badges4dotcom/bsidesperth2025badge/PhysicalBadge/BSides/Game_Data.h

#include "Structures.h"

// Pins for the TFT screen.
#define TFT_CS     15
#define TFT_SCLK   14
#define TFT_DC     27     // Marked as A0 on TFT Display (Rev A: Pin 12, Rev B: 27)
#define TFT_MOSI   13
#define TFT_RST    4

// Pins for the SD Screen.
// Note: Confirmed working pins for RevB.
#define SD_CS   21
#define SD_SCLK 14
#define SD_MISO 12
#define SD_MOSI 13

// Pins for the button inputs.
#define UP_KEY_INPUT    25
#define DOWN_KEY_INPUT  26
#define A_KEY_INPUT     19
#define B_KEY_INPUT     18

// Bitwise registers for the button inputs.
#define UP_KEY_REGISTER   1
#define DOWN_KEY_REGISTER 2
#define A_KEY_REGISTER    4
#define B_KEY_REGISTER    8

// TFT Screen pixel width and height.
#define SCREEN_WIDTH  160
#define SCREEN_HEIGHT 128

// Constants for using a tilemap.
#define TILE_SIZE     				16			// Tile size (both width, and height)
#define TILEMAP_WIDTH 				208			// Width (px) for tilemap
#define TILEMAP_HEIGHT				144			// Height (px) for tilemap
#define TILE_FREEZONE_COLUMN	8				// Tiles in the "Free-zone" do not obstruct the character.
#define TILE_FREEZONE_ROW			4				// Any tile left of the 8th column tile, and above the 4th row, is in hte "free-zone".

#define MAP_SIZE_WIDTH	100						// Width of the map in tiles.
#define MAP_SIZE_HEIGHT	48						// Height of the map in tiles.

#define MAX_LINE_LENGTH   15					// Maximum length of line displayed on screen (used for text-wrapping).
#define MAX_MENUITEMS_ONSCREEN    4		// Maximum number of menu items to display on screen (main menu)
#define MAX_CHALLENGE_SEQUENCE	  60	// Maximum number of sequence items (for the offline challenge)
#define MAX_WIFI_NETWORKS         20	// Maximum number of WiFi networks to list.

#define ICON_SIZE								16		// Size of hte sequence item (offline challenge.)

#define BSIDES_BENNY_LOCATION_X			4		// Benny's character location (x, y) .
#define BSIDES_BENNY_LOCATION_Y			0
#define BSIDES_BENNY2_LOCATION_X		88	// Benny's character location for the petting zoo (x, y) .
#define BSIDES_BENNY2_LOCATION_Y		43

#define MAX_FIREWORKS     					5		// Max fireworks to display on the screen.
#define PARTICLE_LIFETIME 					30	// Firework particles lifetime.

// Game data for the animals in the game.
struct Animal animals[] = {
	{
		"Emu", "Emu", 32/16, 80/16, 1328 / 16, 272 / 16, 0, 0
	},
	{
		"Tasmanian Devil", "Devil", 312/16, 742/16, 1328 / 16, 336 / 16, 0, 0
	},
	{
		"Bob the Human", "Person7", 232/16, 422/16, 1328 / 16, 400 / 16, 0, 0
	},
	{
		"Kangaroo", "Kangaroo", 536/16, 202/16, 1328 / 16, 464 / 16, 0, 0
	},
	{
		"Parrot", "Parrot", 776/16, 678/16, 1328 / 16, 528 / 16, 0, 0
	},
	{
		"Blue Wren", "BlueWren", 596/16, 374/16, 1328 / 16, 592 / 16, 0, 0
	},
	{
		"Cockatoo", "Cockatoo", 1016/16, 54/16, 1328 / 16, 656 / 16, 0, 0
	},
	{
		"Koala", "Koala", 806 / 16, 40 / 16, 1536 / 16, 272 / 16, 0, 0
	},
	{
		"Snake", "Snake", -128 / 16, -128 / 16, 1536 / 16, 336 / 16, 0, 0
	},
	{
		"Spider", "Spider", -128 / 16, -128 / 16, 1536 / 16, 400 / 16, 0, 0
	},
	{
		"Dingo", "Dingo", -128 / 16, -128 / 16, 1536 / 16, 464 / 16, 0, 0
	},
	{
		"Wombat", "Wombat", -128 / 16, -128 / 16, 1536 / 16, 528 / 16, 0, 0
	},
	{
		"Kookaburra", "Kookaburra", -128 / 16, -128 / 16, 1536 / 16, 592 / 16, 0, 0
	},
	{
		"Echidna", "Echidna", -128 / 16, -128 / 16, 1536 / 16, 656 / 16, 0, 0
	}
};

// Game data for the challenges in the game.
const struct Challenge challenges[] = {
	{
		"Two-Timing Ted", "Person6", 56 / 16, 360 / 16, 16, 30, 8,
			{
				{"Person6", "Howdy partner. I'm Two-Timing Ted.",3},
				{"Null", "You be careful. A lot of animals around here have gone missing.",3},
				{"Null", "Anyway, challenge me if you dare!",3},
				{"Null", "",3}
			},
			{
				{"Person6", "Ah, you got me.",3},
				{"Null", "You've completed my challenge.",3},
				{"CyberEchidna", "Looks like your not the only two-timer on the block.",1},
				{"Person6", "I suppose not.",1}
			},
			{
				{"Person6", "Better luck next time.",3},
				{"Null", "",3},
				{"Null", "",3},
				{"Null", "",3}
			},
			{
				{100, "Sometimes if it doesn't work the first time..."},
				{80, "...You need to give it another go."},
				{60, "But timing is key."},
				{20, "You're not going to get the challenge if you stick around this long."}
			}
	},
	{
		"Guiding Gecko", "Person5", 920 / 16, 438 / 16, 20, 30, 9,
			{
				{"Person5", "Why hello there.",3},
				{"Null", "I'd like to GUIDE you through this challenge and this metaverse ..........",3},
				{"Null", "but I can't.",3},
				{"Null", "Good luck!",3}
			},
			{
				{"Person5", "Nice one! You have completed my challenge.",3},
				{"CyberEchidna", "Thanks. Now can you guide me to get the hell outta here??!!",3},
				{"Person5", "Mmmmm ... nah!",3},
				{"CyberEchidna", "Pfffftt!",3}
			},
			{
				{"Person5", "No luck this time.",3},
				{"Null", "Give it another try.",3},
				{"Null", "",3},
				{"Null", "",3}
			},
			{
				{100, "Something ain't right with this GUIDe."},
				{80, "He's a bit questionable."},
				{60, "You may need to find a Postman to fix it."},
				{40, "And post a correct GUIDe."}
			}
	},
	{
		"GP Gertrude", "Person3", 536 / 16, 740 / 16, 28, 30, 10,
			{
				{"Person3", "The doc is in.",3},
				{"Null", "I have the power to help you with this challenge.",3},
				{"Null", "It'd  be a real high for you to complete it.",1},
				{"Null", "",3}
			},
			{
				{"Person3", "You got it! Congratulations!",3},
				{"Null", "You haven't by any chance seen my husband Bob? He's been missing for a few days now.",3},
				{"CyberEchidna", "Ahhhhhh ..... no.",3},
				{"Person3", "Oh ok, I'm sure he'll turn up.",3}
			},
			{
				{"Person3", "No luck with the challenge this time.",3},
				{"Null", "I'm feeling pretty low.", 1},
				{"Null", "Nevermind though, it's like the 2nd time today.", 1},
				{"Null", "", 3}
			},
			{
				{100, "There are only four buttons in this game."},
				{80, "Yet five inputs have been enabled."},
				{60, "The code will give you the answer."},
				{20, "Look at the setup function in BSides.ono."}
			}
	},
	{
		"Sam D. Cornelius", "Person4", 170 / 16, 86 / 16, 42, 30, 11,
			{
				{"Person4", "Good day to you sir.",3},
				{"Null", "I am Sam D. Cornelius.",3},
				{"Null", "I seem to have lost my memories.",1},
				{"Null", "Can you help me find them?",1}
			},
			{
				{"Person4", "Oh, there they are. Thank you.",1},
				{"Person4", "You got the challenge.",3},
				{"Null", "Now on your way you.",3},
				{"CyberEchidna", "Farewell Sam D. Cornelius. I hope to always be in your memories.",1}
			},
			{
				{"Person4", "You didn't get the challenge this time.",3},
				{"Null", "Just like the animals around here, my memories seem to be non existant.",1},
				{"Null", "I'll be here all day.",1},
				{"Null", "",3}
			},
			{
				{100, "Sometimes this character goes by SD Cornelius"},
				{80, "You should check to see if he's given you a file"},
				{60, "And see if the file contents is correct"},
				{10, ""}
			}
	},
	{
		"Hidden Harriette", "Person2", 1096 / 16, 230 / 16, 50, 30, 12,
			{
				{"Person2", "How did you find me?",3},
				{"Null", "I thought I've been hiding better than all the animals around here.",3},
				{"Null", "My friend Bob was digging into where all the animals have gone, and now he's missing too.",3},
				{"Null", "Well, anyway, let's see if you can get my challenge.",3}
			},
			{
				{"Person2", "Gosh darn it.",3},
				{"Null", "Maybe I need to get better at hiding.",1},
				{"Null", "Well done on completing my challenge.",3},
				{"CyberEchidna", "Thanks. I was hide and seek champion three years running.",1}
			},
			{
				{"Person2", "No luck with the challenge this time.",3},
				{"Person2", "They don't call me Hidden Harriette for nothing.",1},
				{"Null", "",3},
				{"Null", "",3}
			},
			{
				{100,"This one is going to need a Postman"},
				{80,"Or a bug fix, recompile, and download."},
				{40,"In any case, it could get messy."},
				{10,""}
			}
	}
};

// The map for the game.
const int gameMap[MAP_SIZE_HEIGHT][MAP_SIZE_WIDTH] = {
{22,22,22,23,-1,78,80,13,14,15,16,17,-1,-1,-1,-1,-1,-1,-1,-1,44,45,46,-1,-1,-1,-1,-1,-1,-1,-1,-1,-1,-1,-1,-1,-1,-1,-1,-1,-1,-1,-1,-1,-1,78,80,-1,-1,-1,-1,-1,-1,-1,-1,-1,-1,-1,-1,-1,-1,91,79,79,79,79,79,79,79,79,79,79,79,79,79,79,79,79,79,93,78,80,-1,-1,-1,-1,-1,-1,-1,-1,-1,-1,-1,-1,-1,-1,-1,-1,-1,-1},
{35,35,35,36,-1,91,93,26,27,28,29,30,-1,-1,-1,-1,-1,-1,-1,-1,57,58,59,-1,-1,-1,-1,-1,-1,-1,-1,-1,-1,-1,-1,-1,-1,-1,-1,-1,-1,-1,-1,-1,-1,91,93,-1,-1,-1,-1,-1,-1,44,45,46,-1,-1,-1,-1,-1,91,92,105,105,105,105,105,105,105,105,105,105,105,105,105,105,105,92,93,91,93,-1,-1,-1,-1,-1,-1,-1,-1,-1,-1,-1,-1,-1,-1,-1,-1,-1,-1},
{-1,34,35,36,-1,91,93,39,40,41,42,43,-1,-1,-1,-1,-1,-1,-1,-1,70,71,72,-1,-1,-1,-1,-1,-1,-1,-1,-1,-1,-1,-1,-1,-1,-1,-1,-1,-1,-1,-1,-1,-1,91,93,-1,-1,-1,-1,-1,-1,57,58,59,-1,-1,-1,-1,-1,91,93,-1,-1,-1,-1,-1,-1,-1,-1,-1,-1,-1,-1,44,45,46,91,93,91,93,-1,-1,-1,-1,-1,-1,-1,-1,-1,-1,-1,-1,-1,-1,-1,-1,-1,-1},
{-1,34,35,36,-1,91,93,52,53,54,55,56,60,-1,-1,-1,-1,-1,-1,-1,-1,-1,-1,-1,-1,21,22,22,22,22,22,22,22,22,22,22,22,22,22,22,22,22,23,-1,-1,91,93,-1,-1,-1,-1,-1,-1,70,71,72,-1,-1,-1,-1,-1,91,93,-1,-1,-1,-1,-1,-1,-1,-1,-1,-1,-1,-1,57,58,59,91,93,91,93,-1,-1,-1,-1,-1,-1,-1,-1,-1,-1,-1,-1,-1,-1,-1,-1,-1,-1},
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
{-1,34,35,36,-1,-1,-1,-1,-1,-1,-1,-1,-1,-1,-1,-1,78,80,34,35,36,-1,70,71,72,-1,-1,-1,-1,-1,-1,-1,-1,-1,-1,-1,-1,-1,-1,-1,-1,-1,-1,91,93,-1,34,35,25,48,48,48,48,48,48,48,48,48,49,-1,-1,-1,91,93,-1,-1,91,93,-1,-1,-1,-1,57,58,59,91,93,34,35,36,91,92,105,105,105,105,92,93,-1,-1,-1,-1,91,92,105,105,105,105,92,93},
{-1,34,35,36,-1,-1,78,80,-1,-1,-1,-1,-1,-1,-1,-1,91,93,34,35,12,22,22,22,22,22,22,22,22,22,22,22,22,22,22,22,22,22,22,23,-1,-1,-1,91,93,-1,47,48,49,-1,-1,-1,-1,-1,-1,-1,-1,-1,-1,-1,-1,-1,91,92,79,79,92,93,-1,-1,-1,-1,70,71,72,91,93,34,35,36,91,93,-1,-1,-1,-1,91,93,-1,-1,-1,-1,91,93,-1,-1,-1,-1,91,93},
{-1,34,35,36,-1,-1,91,93,-1,-1,-1,-1,-1,-1,-1,-1,91,93,34,35,35,35,35,35,35,35,35,35,35,35,35,35,35,35,35,35,35,35,35,36,-1,-1,-1,91,93,-1,-1,-1,-1,-1,-1,-1,78,80,-1,-1,-1,-1,-1,-1,-1,-1,104,105,105,105,105,106,-1,-1,-1,-1,-1,-1,-1,91,93,34,35,36,91,93,-1,-1,-1,-1,91,93,-1,-1,-1,-1,91,93,-1,-1,-1,-1,91,93},
{-1,34,35,36,-1,-1,91,93,-1,-1,-1,-1,-1,-1,-1,-1,91,93,47,48,48,48,48,48,48,48,48,48,48,48,48,48,48,48,48,48,48,24,35,36,-1,-1,-1,91,93,-1,-1,-1,-1,-1,-1,-1,91,93,-1,-1,-1,-1,-1,-1,-1,-1,-1,-1,-1,-1,-1,-1,-1,-1,-1,-1,-1,-1,-1,91,93,34,35,36,91,92,79,79,79,79,92,93,-1,-1,-1,-1,91,92,79,79,79,79,92,93},
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
};

// Definitions required for Online Challenges.
char* GAME_WEB_URL = "badge.bsidesperth.com.au";
char* GAME_ROOT_CERTIFICATE = \
"-----BEGIN CERTIFICATE-----\n" \
"MIIEGzCCAwOgAwIBAgIULYVISFG3QsBjY+rdPtSzc/bA4hQwDQYJKoZIhvcNAQEL\n" \
"BQAwgZwxCzAJBgNVBAYTAkFVMRowGAYDVQQIDBFXZXN0ZXJuIEF1c3RyYWxpYTEO\n" \
"MAwGA1UEBwwFUGVydGgxFTATBgNVBAoMDEJTaWRlcyBQZXJ0aDEhMB8GA1UEAwwY\n" \
"YmFkZ2UuYnNpZGVzcGVydGguY29tLmF1MScwJQYJKoZIhvcNAQkBFhhhZG1pbkBi\n" \
"c2lkZXNwZXJ0aC5jb20uYXUwHhcNMjUxMDE3MDE1ODE3WhcNMjYxMDE3MDE1ODE3\n" \
"WjCBnDELMAkGA1UEBhMCQVUxGjAYBgNVBAgMEVdlc3Rlcm4gQXVzdHJhbGlhMQ4w\n" \
"DAYDVQQHDAVQZXJ0aDEVMBMGA1UECgwMQlNpZGVzIFBlcnRoMSEwHwYDVQQDDBhi\n" \
"YWRnZS5ic2lkZXNwZXJ0aC5jb20uYXUxJzAlBgkqhkiG9w0BCQEWGGFkbWluQGJz\n" \
"aWRlc3BlcnRoLmNvbS5hdTCCASIwDQYJKoZIhvcNAQEBBQADggEPADCCAQoCggEB\n" \
"AKhhTlis1jlzda90e7ueb6dc7XlPJJdcV3fNfwi2+jSr2BVRGpUgWcsspCC+cxSy\n" \
"d9wv0Lr60v+ccpxxLAPtAxR48KrmVZs4FraxJTnCfyebFnHT4p/vNmBaNvrnKZXQ\n" \
"aHe+EBjNE14J4OXet9EannqkWA0cuOIMqQiDGYAGwJFSP6bgIh6L1F0s+eXr8F2l\n" \
"1OomFlVebRJ0Iu89hi7E+KohI/cqvv8UgaqLgF9rTgyxmdlCf7U33GKIf7Cq0p24\n" \
"34KhDgse64Ge2AFpZv3kpGbAy8nSmLG37LdcSD9Df2L5ysOM5XJGxwYmwmgj7uhI\n" \
"oHVl72/a5a3N3i5fjx2Jr8kCAwEAAaNTMFEwHQYDVR0OBBYEFGDpsNiHHIQKmhDM\n" \
"rSFdu90t3cfrMB8GA1UdIwQYMBaAFGDpsNiHHIQKmhDMrSFdu90t3cfrMA8GA1Ud\n" \
"EwEB/wQFMAMBAf8wDQYJKoZIhvcNAQELBQADggEBAG52x7Ly3pixucy2iKD4GfUj\n" \
"E3uNZZVUNSY9omg1DKZt+BZXB9MVlwvJ+VYmdatSi+gBP2nz50ISpz4aFAHT3ex4\n" \
"35GU/YALRiUQhTQ+EmiNxQ2EjBQG7hgj/c6E89IHbDqQdDXe7zclo4SmYPuFo4uX\n" \
"LYn917K0cE391gtj1vxajw/HXRkyWZlv0WdffnCzFilfy006QLs9qEy8K8OY9rnk\n" \
"q+Eoritwj3cVzLdpvZpUnEZrOsMlEKrMP8DsWu/PaCw9nSybek5f2oA1topLOCTl\n" \
"iZ/kkfc6/mhgGSVODRJQaog8xuqh+6XDQ8zSFME1S6OuooP6ak2peZ7/ojES16U=\n" \
"-----END CERTIFICATE-----\n";
#define CHALLENGE_POLL_TIME		30			// The period to query the online server for online challenge success/failure.

// The available GPIO which haven't been assigned to anything else.
const int available_gpio[] = {
	1, 2, 3, 5, 16, 17, 22, 23, 32, 33, 34, 35, 36, 39
};
#define GPIO_CHALLENGE_PTR	1			
