badges4dotcom/bsidesperth2025badge/VirtualBadge/Episode2/Game_Data.js

// Key input bitmasks
const UP_KEY_REGISTER = 1;
const DOWN_KEY_REGISTER = 2;
const A_KEY_REGISTER = 4;
const B_KEY_REGISTER = 8;

const NUM_KEYS = 4;

// TFT screen dimensions
const SCREEN_WIDTH = 160;
const SCREEN_HEIGHT = 128;

// Tilemap constants
const TILE_SIZE = 16;             // Tile size (both width and height)
const TILEMAP_WIDTH = 208;        // Width in pixels for tilemap
const TILEMAP_HEIGHT = 144;       // Height in pixels for tilemap
const TILE_FREEZONE_COLUMN = 8;   // Columns in "free-zone"
const TILE_FREEZONE_ROW = 4;      // Rows in "free-zone"

// Map size in tiles
const MAP_SIZE_WIDTH = 100;
const MAP_SIZE_HEIGHT = 48;

// Text and menu constants
const MAX_LINE_LENGTH = 14;           // Max characters per line
const MAX_MENUITEMS_ONSCREEN = 4;     // Max menu items displayed
const MAX_CHALLENGE_SEQUENCE = 60;    // Max sequence items (offline challenge)
const MAX_WIFI_NETWORKS = 20;         // Max WiFi networks listed

// Icon size for offline challenge
const ICON_SIZE = 16;

// Benny's locations
const BSIDES_BENNY_LOCATION_X = 0;
const BSIDES_BENNY_LOCATION_Y = 40;
const BSIDES_BENNY2_LOCATION_X = 94;
const BSIDES_BENNY2_LOCATION_Y = 43;

// Fireworks / particles
const MAX_FIREWORKS = 5;
const PARTICLE_LIFETIME = 30;

const items = [
  new Item("PKI Certificate", "PKICertificate", 6, 12, 2, 45),
  new Item("Hardware Security Module", "HSM", 61, 6, 3, 45),
  new Item("Crypto Wallet", "CryptoWallet", 67, 46, 4, 45),
  new Item("Floppy Disk", "FloppyDisk", 1, 5, 5, 45),
  new Item("Laser Pointer", "LaserPointer", 45, 23, 6, 45),
  new Item("Credit Card", "CreditCard", 64, 1, 7, 45),
  new Item("LCD Screen", "LCDScreen", 1, 34, 8, 45),
  new Item("ESP32", "ESP32", 85, 20, 9, 45),
  new Item("High Powered GPU", "HighPoweredGPU", 91, 34, 2, 47),
  new Item("BSides Perth 2025 Badge", "Badge", 99, 32, 3, 47),
  new Item("Prism", "Prism", 97, 24, 4, 47),
  new Item("Flux Capacitor", "FluxCapacitor", -8, -8, 5, 47),
  new Item("2x AA Batteries", "Batteries", -8, -8, 6, 47),
  new Item("486 Computer", "486Computer", -8, -8, 7, 47),
  new Item("Instruction Manual", "Manual", -8, -8, 8, 47),
  new Item("Game Controller", "GameController", -8, -8, 9, 47)
];

const challenges = [
  new Challenge(
    "Peter", "Person6", 3, 22, 50, 30, 11,
    [
      new Dialogue("Person6", "Hi there, my name is Peter.", 3),
      new Dialogue("Null", "Have you heard the rumour?", 3),
      new Dialogue("Null", "Benny is building some kind of supercomputer.", 3),
      new Dialogue("Null", "Anyway, are you ready to challenge me?", 3)
    ],
    [
      new Dialogue("Person6", "Oh, you got the challenge.", 3),
      new Dialogue("Null", "I've misplaced my credit card. Have you seen it?", 3),
      new Dialogue("CyberEchidna", "Hmmmm.....no.", 3),
      new Dialogue("Null", "", 3)
    ],
    [
      new Dialogue("Person6", "Better luck next time.", 3),
      new Dialogue("Null", "", 3),
      new Dialogue("Null", "", 3),
      new Dialogue("Null", "", 3)
    ],
    [
      new Hint(100, ""),
      new Hint(80, ""),
      new Hint(60, ""),
      new Hint(20, "")
    ]
  ),
  new Challenge(
    "Joe", "Person5", 57, 27, 42, 30, 12,
    [
      new Dialogue("Person5", "Why hello there.", 3),
      new Dialogue("Null", "Neat badge. Where did you get that?", 3),
      new Dialogue("CyberEchidna", "Oh, this thing? From the BSides Perth 2025 conference.", 3),
      new Dialogue("Person5", "Nice, I'm jelly.", 3)
    ],
    [
      new Dialogue("Person5", "Good one! You have completed my challenge.", 3),
      new Dialogue("Null", "It must have been the luck of the badge.", 3),
      new Dialogue("CyberEchidna", "Yep, it's the best.", 3),
      new Dialogue("Person5", "Good luck out there Cyber Echidna.", 3)
    ],
    [
      new Dialogue("Person5", "No luck this time.", 3),
      new Dialogue("Null", "Maybe next time.", 3),
      new Dialogue("Null", "", 3),
      new Dialogue("Null", "", 3)
    ],
    [
      new Hint(100, ""),
      new Hint(80, ""),
      new Hint(60, ""),
      new Hint(40, "")
    ]
  ),
  new Challenge(
    "Elena", "Person3", 33, 46, 28, 30, 13,
    [
      new Dialogue("Person3", "Oh, hi!", 3),
      new Dialogue("Null", "Aren't you a cute widdle Cyber Echidna?", 3),
      new Dialogue("CyberEchidna", "Let's just get the challenge over and done with.", 3),
      new Dialogue("Null", "", 3)
    ],
    [
      new Dialogue("Person3", "Well done on completing my challenge.", 3),
      new Dialogue("Null", "Good luck on finding those items.", 3),
      new Dialogue("Null", "", 3),
      new Dialogue("Null", "", 3)
    ],
    [
      new Dialogue("Person3", "No luck with the challenge this time.", 3),
      new Dialogue("Null", "Looking forward to seeing you next time cute widdle Cyber Echidna.", 3),
      new Dialogue("Null", "", 3),
      new Dialogue("Null", "", 3)
    ],
    [
      new Hint(100, ""),
      new Hint(80, ""),
      new Hint(60, ""),
      new Hint(20, "")
    ]
  ),
  new Challenge(
    "Bob", "Person7", 15, 5, 20, 30, 14,
    [
      new Dialogue("Person7", "Remember me Cyber Echidna??!.", 3),
      new Dialogue("Null", "You collected me up, and took me to the BSides petting zoo.", 3),
      new Dialogue("Null", "That was over 12 years ago.", 3),
      new Dialogue("Null", "Now you're going to pay with this challenge.", 3)
    ],
    [
      new Dialogue("Person7", "Oh, you won this challenge.", 3),
      new Dialogue("Person7", "I forgive you Cyber Echidna for what happened 12 years ago.", 3),
      new Dialogue("Null", "I was only in the petting zoo until you left, and then I snuck out anyway.", 3),
      new Dialogue("CyberEchidna", "Kthxbye., ", 3)
    ],
    [
      new Dialogue("Person7", "You didn't get the challenge this time.", 3),
      new Dialogue("Null", "Maybe its time I take you to the BSides petting zoo.", 3),
      new Dialogue("Null", "Hmmm, its late in the day, maybe next time.", 3),
      new Dialogue("Null", "", 3)
    ],
    [
      new Hint(100, ""),
      new Hint(80, ""),
      new Hint(60, ""),
      new Hint(10, "")
    ]
  ),
  new Challenge(
    "Cynthia", "Person2", 68, 14, 16, 30, 15,
    [
      new Dialogue("Person2", "My name is Cynthia. Welcome to my home.", 3),
      new Dialogue("Null", "So you're the Cyber Echidna everyone is talking about?", 3),
      new Dialogue("Null", "I thought you were a folklore.", 3),
      new Dialogue("Null", "Well, anyway, let's see if you're as good as they say you are.", 3)
    ],
    [
      new Dialogue("Person2", "Goodness gracious.", 3),
      new Dialogue("Null", "The folklore of 'Cyber Echidna' was true!", 3),
      new Dialogue("Null", "Take this item as a tribute.", 3),
      new Dialogue("Null", "", 3)
    ],
    [
      new Dialogue("Person2", "No luck with the challenge this time.", 3),
      new Dialogue("Null", "Y'all come back now.", 3),
      new Dialogue("Null", "", 3),
      new Dialogue("Null", "", 3)
    ],
    [
      new Hint(100,""),
      new Hint(80,""),
      new Hint(40,""),
      new Hint(10,"")
    ]
  )
];


const gameMap = [
[-1,-1,91,93,-1,-1,-1,-1,-1,-1,-1,-1,13,14,15,16,17,-1,-1,-1,-1,21,22,22,22,22,22,22,22,22,22,22,22,22,22,22,22,22,22,22,22,22,22,22,22,22,22,22,22,22,22,22,22,22,22,22,22,22,22,22,22,23,-1,-1,-1,-1,-1,-1,44,45,46,-1,-1,-1,-1,-1,-1,-1,-1,-1,-1,-1,-1,-1,-1,-1,-1,-1,-1,-1,-1,-1,-1,-1,-1,-1,-1,44,45,46],
[-1,-1,91,93,-1,-1,-1,-1,-1,-1,-1,-1,26,27,28,29,30,-1,-1,-1,-1,34,35,35,35,35,35,35,35,35,35,35,35,35,35,35,35,35,35,35,35,35,35,35,35,35,35,35,35,35,35,35,35,35,35,35,35,35,35,35,35,36,-1,-1,-1,-1,-1,-1,57,58,59,-1,-1,-1,-1,-1,-1,-1,-1,-1,-1,-1,-1,-1,-1,-1,-1,-1,-1,-1,-1,-1,-1,-1,-1,-1,-1,57,58,59],
[-1,-1,91,92,79,79,79,79,79,80,-1,-1,39,40,41,42,43,-1,44,45,46,34,35,25,48,48,48,48,48,48,48,48,48,48,48,48,48,48,48,48,48,48,48,48,48,48,48,48,48,48,48,48,48,48,48,48,48,48,48,48,48,49,-1,-1,-1,-1,-1,-1,70,71,72,-1,-1,-1,-1,-1,-1,-1,-1,-1,-1,-1,-1,-1,-1,-1,-1,-1,-1,-1,-1,-1,-1,-1,-1,-1,-1,70,71,72],
[-1,-1,104,105,105,105,105,105,105,106,-1,-1,52,53,54,55,56,60,57,58,59,34,35,36,-1,-1,-1,-1,-1,-1,-1,-1,-1,-1,-1,-1,-1,-1,-1,-1,-1,-1,-1,-1,-1,-1,-1,-1,-1,-1,-1,-1,-1,-1,-1,-1,-1,-1,-1,-1,-1,-1,-1,-1,-1,-1,-1,-1,-1,-1,-1,-1,-1,-1,-1,-1,-1,-1,-1,-1,-1,-1,-1,-1,-1,-1,-1,-1,-1,-1,-1,-1,-1,-1,-1,-1,-1,-1,-1,-1],
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
const CHALLENGE_POLL_TIME = 30;

// The available GPIO pins which haven't been assigned to anything else
const available_gpio = [1, 2, 3, 5, 16, 17, 22, 23, 32, 33, 34, 35, 36, 39];

// The GPIO pin used for the challenge pointer
const GPIO_CHALLENGE_PTR = 1; // Could also be 3
